AKAMEDIASYSTEM/WEFT/WEFT-photos/electrovibration-experiments3.jpg

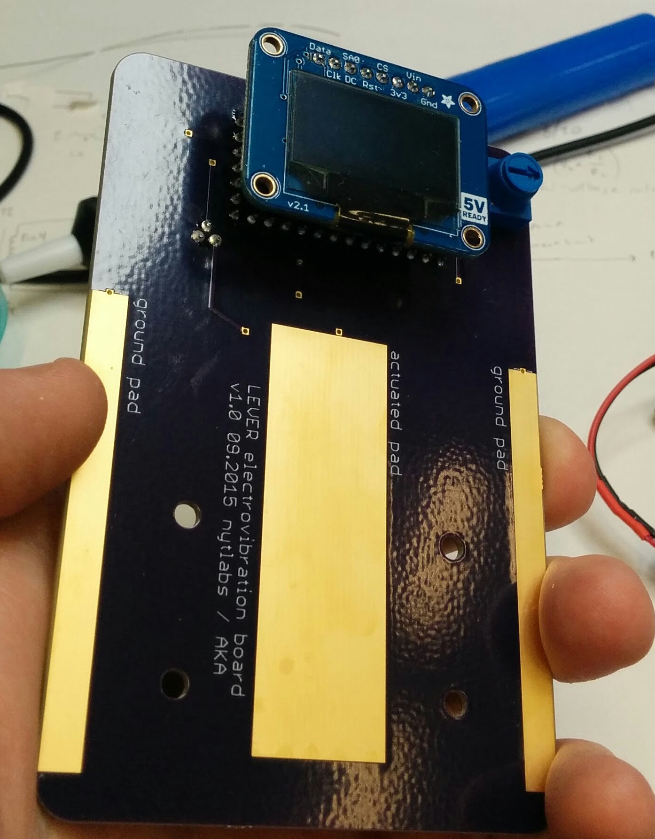
WEFT-photos/electrovibration-experiments3.jpg
