AKAMEDIASYSTEM/WEFT/weft-teensy-slave/comms.ino

void receiveEvent(int howMany) {
 digitalWrite(LED,LOW);
  byte c = 0;
  byte d = 255;
  while (Wire.available()) {
    c = Wire.read(); // mode byte, like encMode  {"FREQ", "AMP", "WAVE", "DUTY"};
    d = Wire.read(); // value byte, 0-255
  }

  switch (int(c)) {
    case 0: // FREQ
      phaseOffset = constrain(floatmap(int(d), 0, 255, minFreq, maxFreq), minFreq, maxFreq);
      break;
    case 1: // AMP
      DACamplitude = constrain(floatmap(int(d), 0.0, 255, minAmpl, maxAmpl), minAmpl, maxAmpl);
      break;
    case 2: // WAVE
      waveType = constrain(d, 0, 4); // here d must be between 0 and 4 {"SINE", "SQUARE", "D_SAW", "A_SAW", "NOISE"}
      break;
    case 3: // DUTY
      dutyCycle = constrain(floatmap(int(d), 0.0, 255, minDuty, maxDuty), minDuty, maxDuty);
      break;
    default:
      phaseOffset = constrain(floatmap(int(d), 0, 255, minFreq, maxFreq), minFreq, maxFreq);
      break;
  }
  digitalWrite(LED,HIGH);
}
